simpleairquality/Device-Models/assets/09.jpg

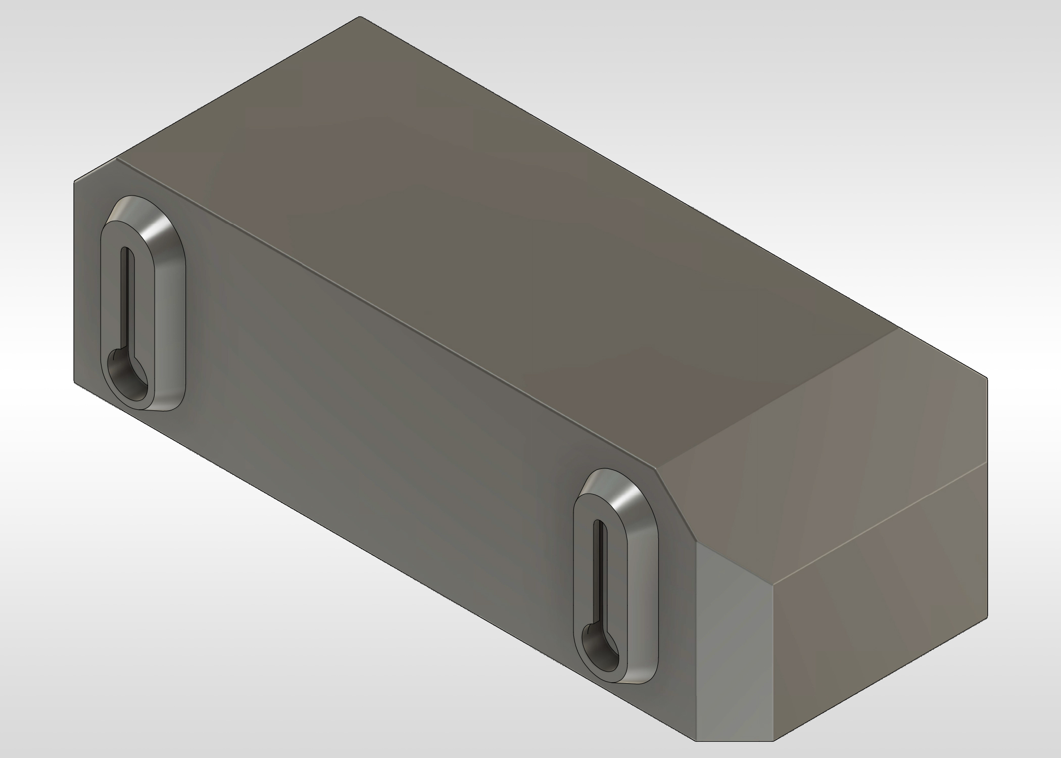
assets/09.jpg
